ArnieX/swifitch/Images/Software/physical_switch.png

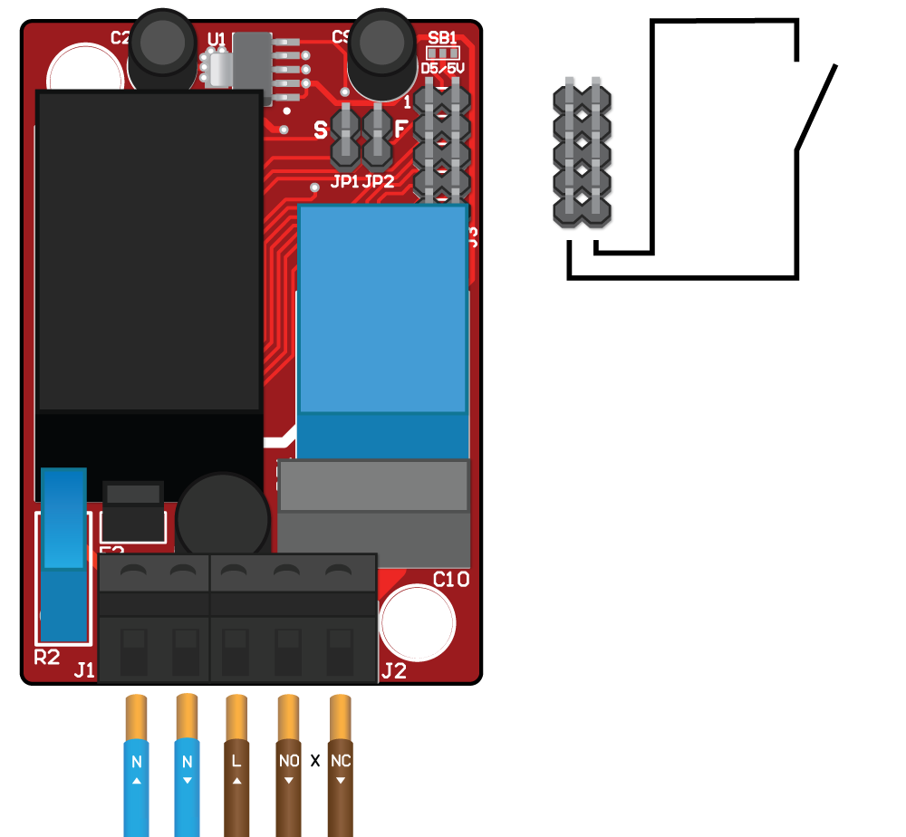
Images/Software/physical_switch.png
