ArnieX/swifitch/Images/Software/swifitch_sw_config_1.png

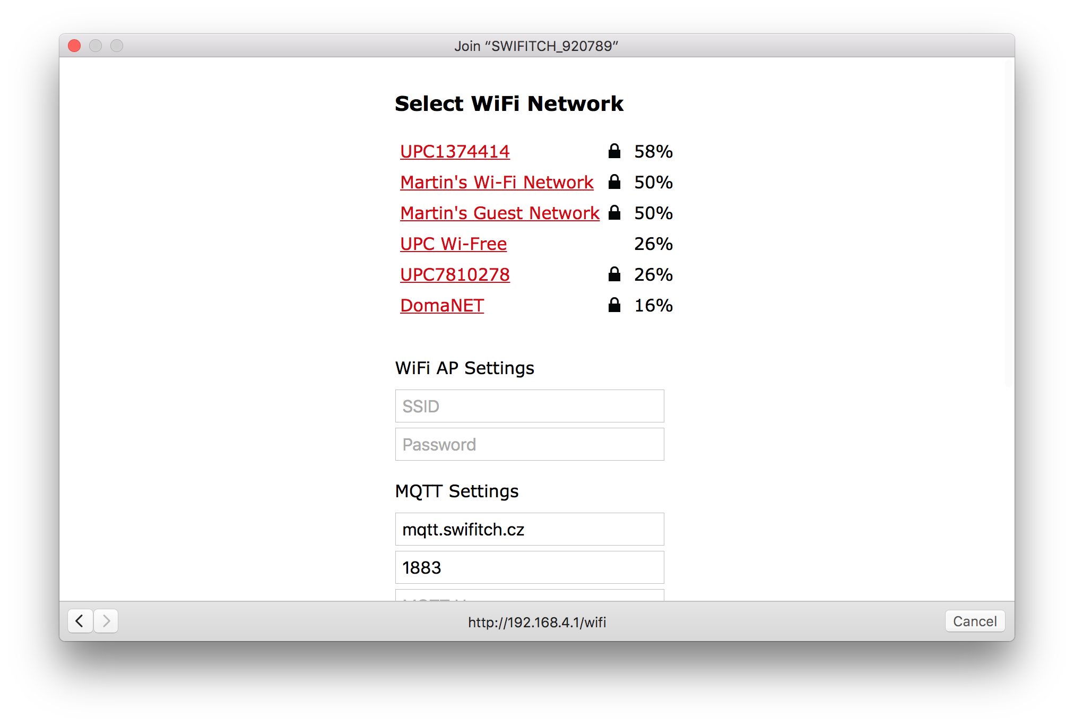
Images/Software/swifitch_sw_config_1.png
