ArnieX/swifitch/Images/Software/swifitch_sw_config_1_new.png

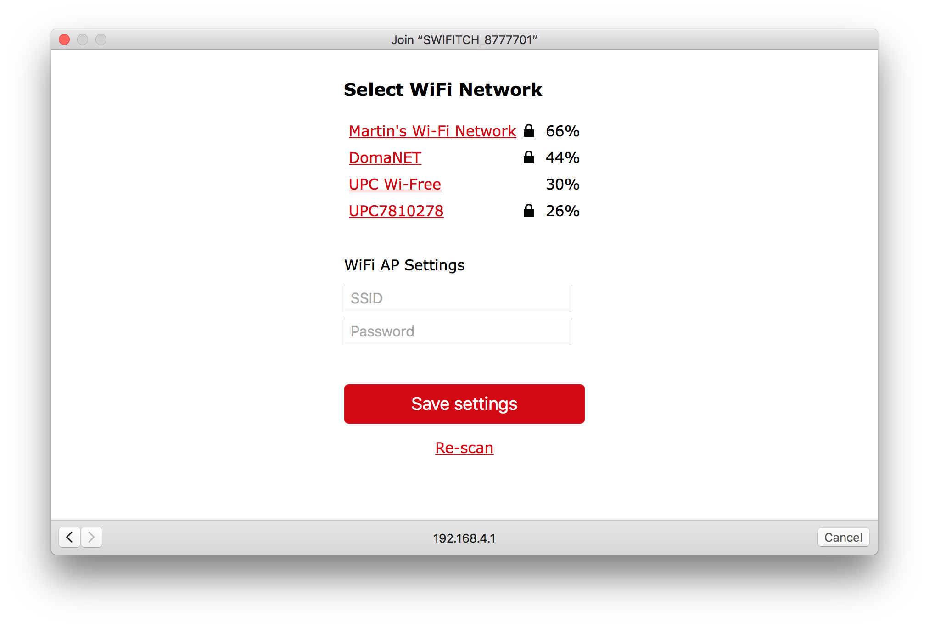
Images/Software/swifitch_sw_config_1_new.png
