ArnieX/swifitch/Images/Software/swifitch_sw_config_2.png

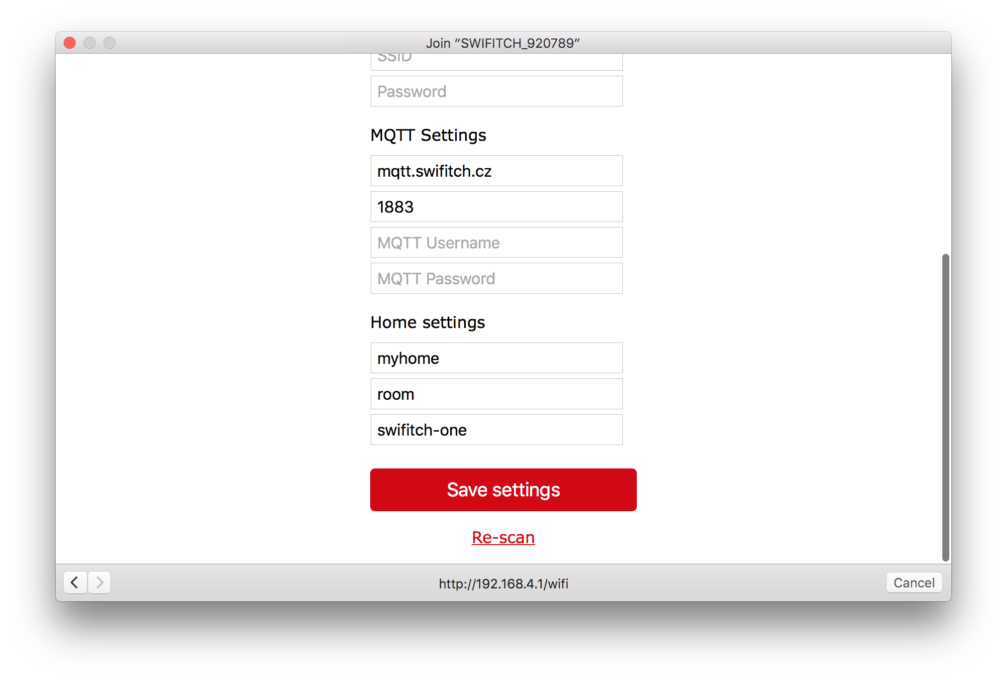
Images/Software/swifitch_sw_config_2.png
