ArnieX/swifitch/Images/Software/swifitch_sw_config_root.png

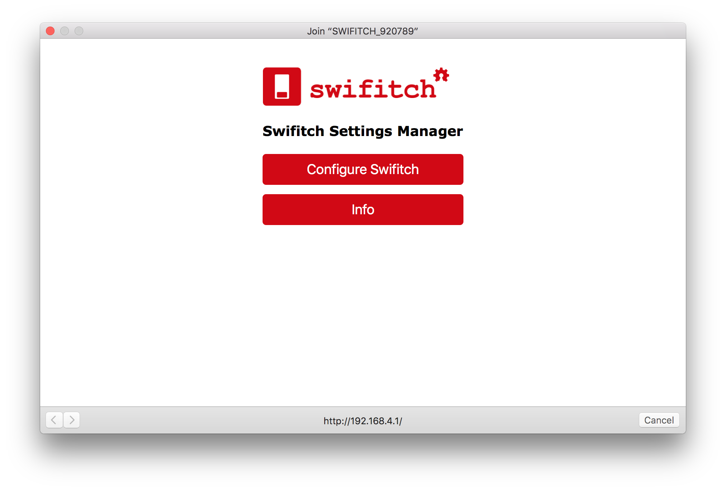
Images/Software/swifitch_sw_config_root.png
