ArnieX/swifitch/Images/Software/swifitch_sw_web_configuration_portal_new.png

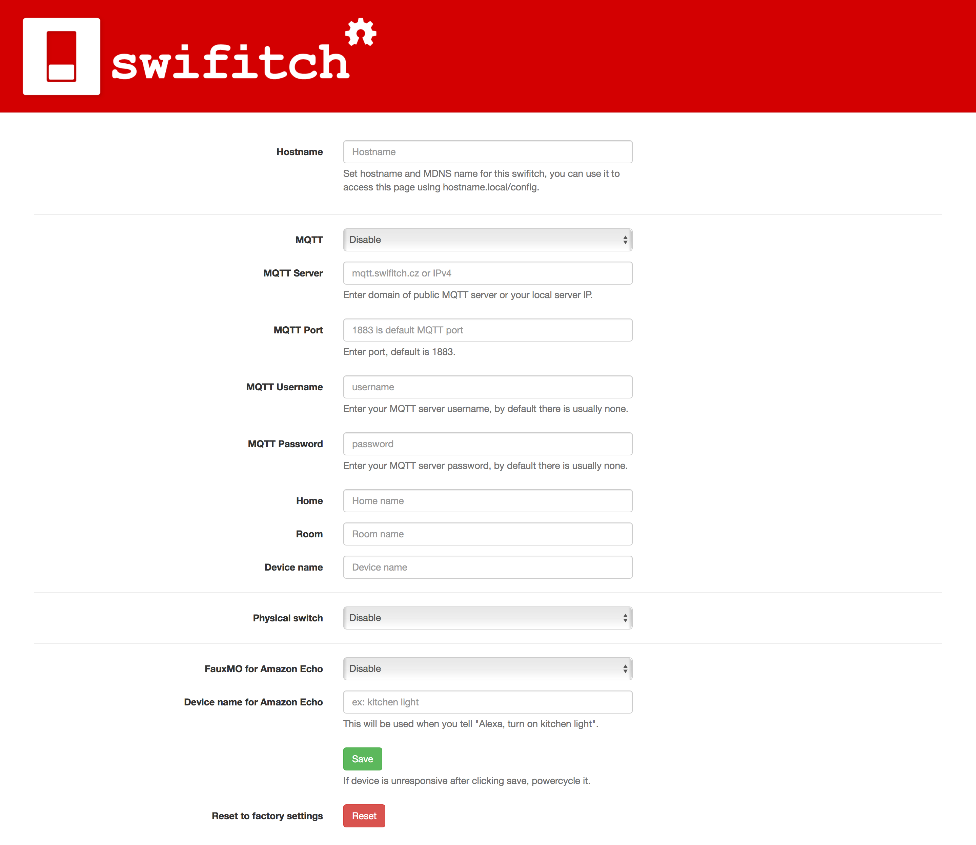
Images/Software/swifitch_sw_web_configuration_portal_new.png
