ArnieX/swifitch/Images/swifitch_box_transp.png

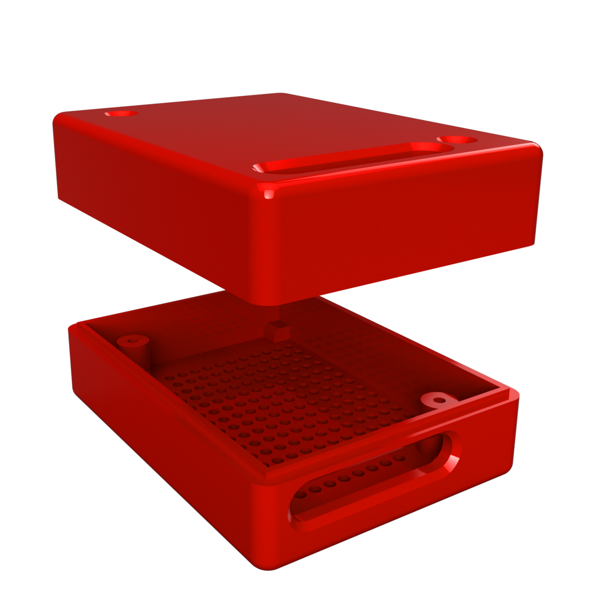
Images/swifitch_box_transp.png
