ArnieX/swifitch/Images/Parts/Gray_BG_Parts/MCP1825T-3302E-DC.png

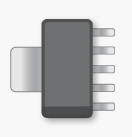
Images/Parts/Gray_BG_Parts/MCP1825T-3302E-DC.png
