ArnieX/swifitch/Images/Swifitch_PCB_parts_list.png

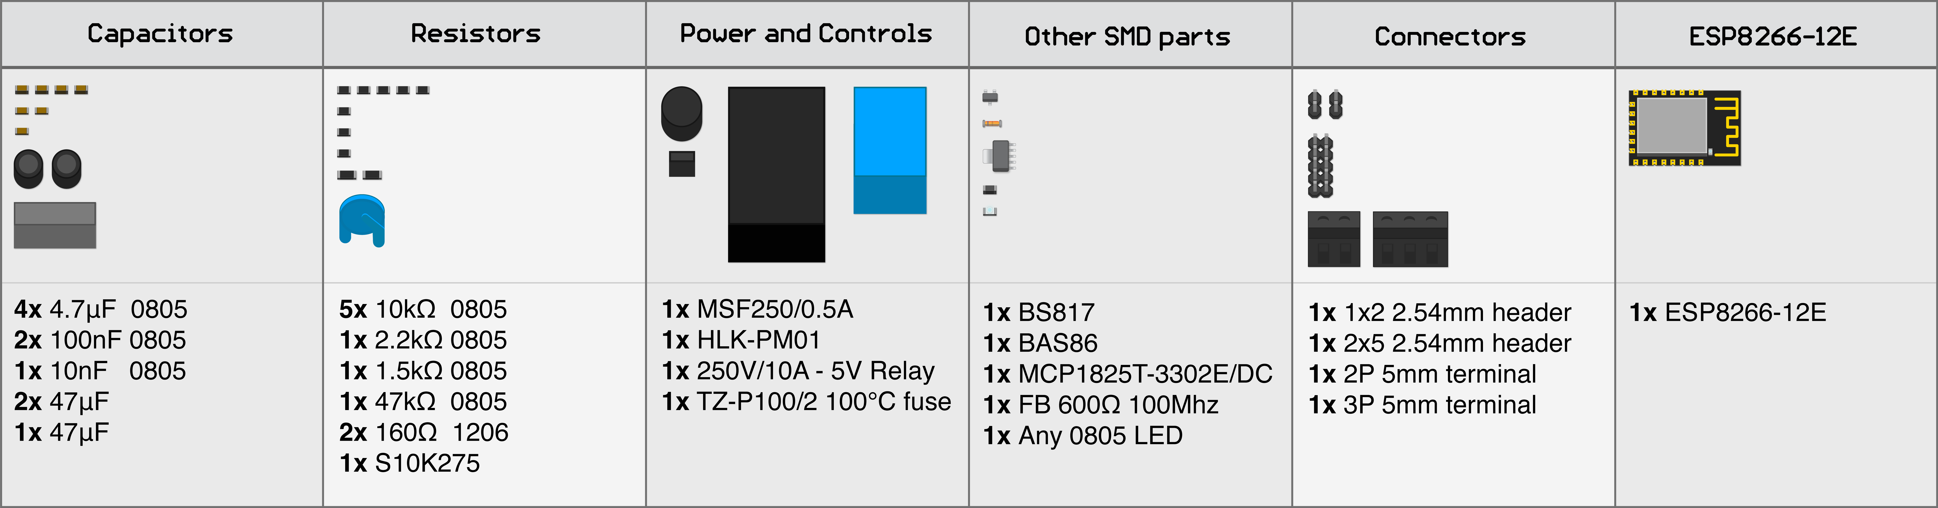
Images/Swifitch_PCB_parts_list.png
